dl2sba/hamware-interface/images/DSCF4106.jpg

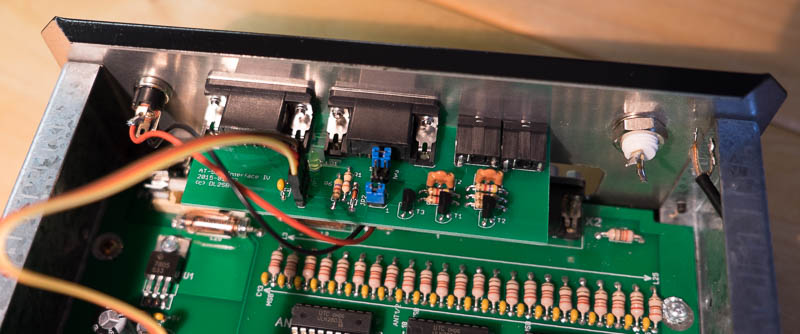
images/DSCF4106.jpg
