dl2sba/hamware-interface/images/DSCF4109.jpg

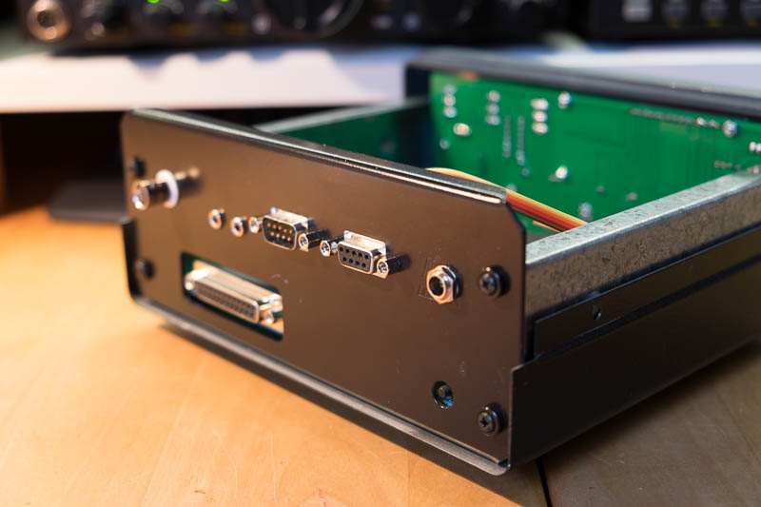
images/DSCF4109.jpg
